ThAUJAS/H.E.D.A.S-Exoskeleton-glove-sensor-/image/45_wrist.png

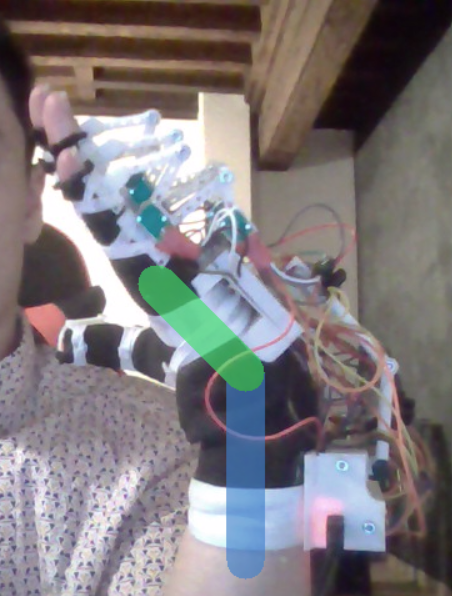
image/45_wrist.png
