ThAUJAS/H.E.D.A.S-Exoskeleton-glove-sensor-/image/_30_wrist.png

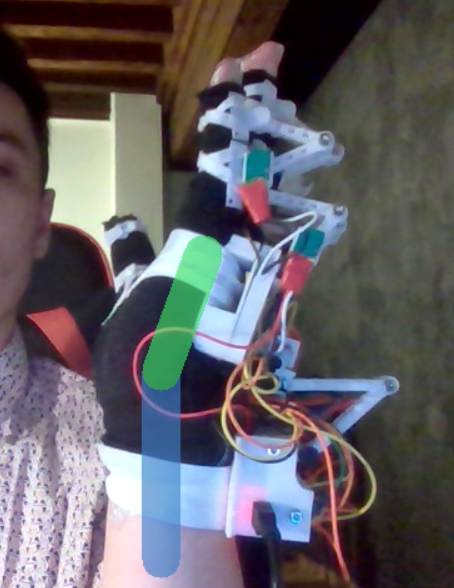
image/_30_wrist.png
