ThAUJAS/H.E.D.A.S-Exoskeleton-glove-sensor-/image/_45_wrist.png

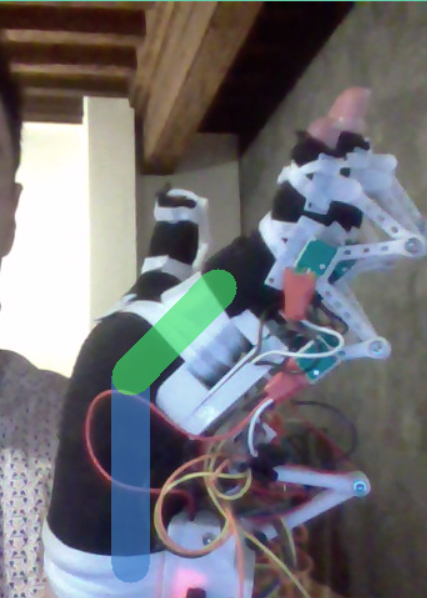
image/_45_wrist.png
