ThAUJAS/H.E.D.A.S-Exoskeleton-glove-sensor-/image/open_face.png

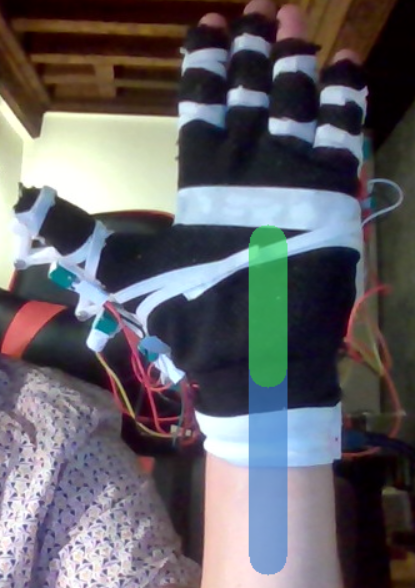
image/open_face.png
