ThAUJAS/H.E.D.A.S-Exoskeleton-glove-sensor-/STL/pin PIP v4.stl

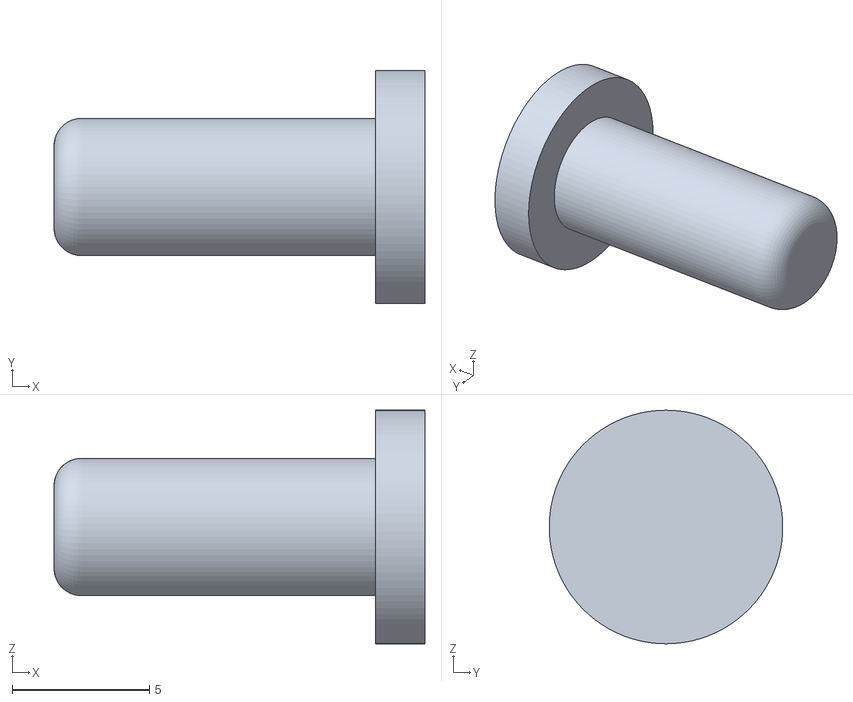
[picture p82: CAD file, 2021-08-12]
STL/pin PIP v4.stl
13.5 x 8.49 x 8.50
