ThAUJAS/H.E.D.A.S-Exoskeleton-glove-sensor-/STL/wire holder wrist z v6.stl

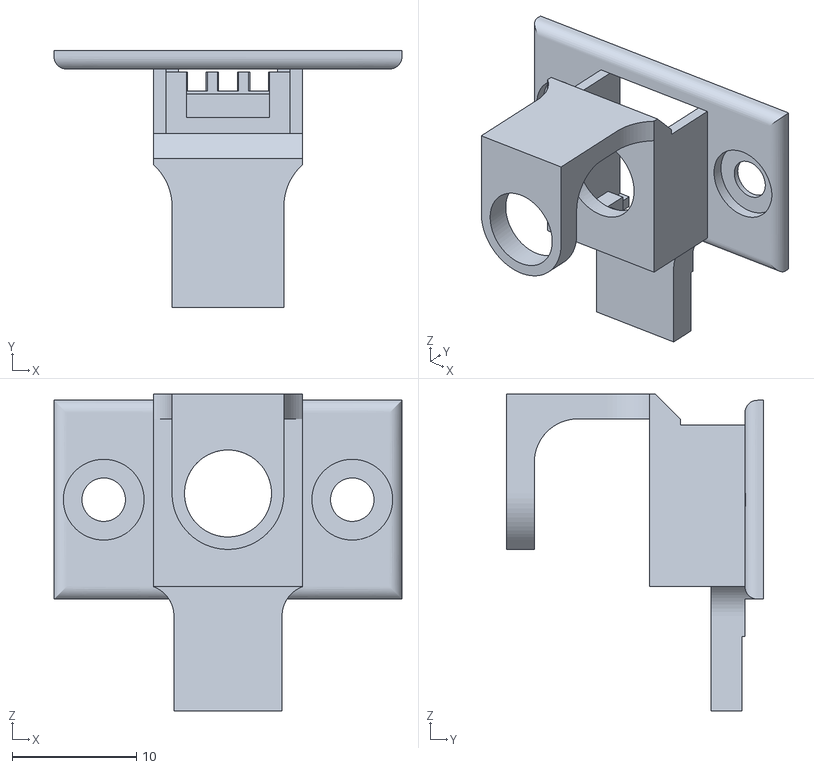
[picture p83: CAD file, 2021-08-12]
STL/wire holder wrist z v6.stl
28.0 x 20.7 x 25.5
