ThAUJAS/H.E.D.A.S-Exoskeleton-glove-sensor-/STL/cover arduino.stl

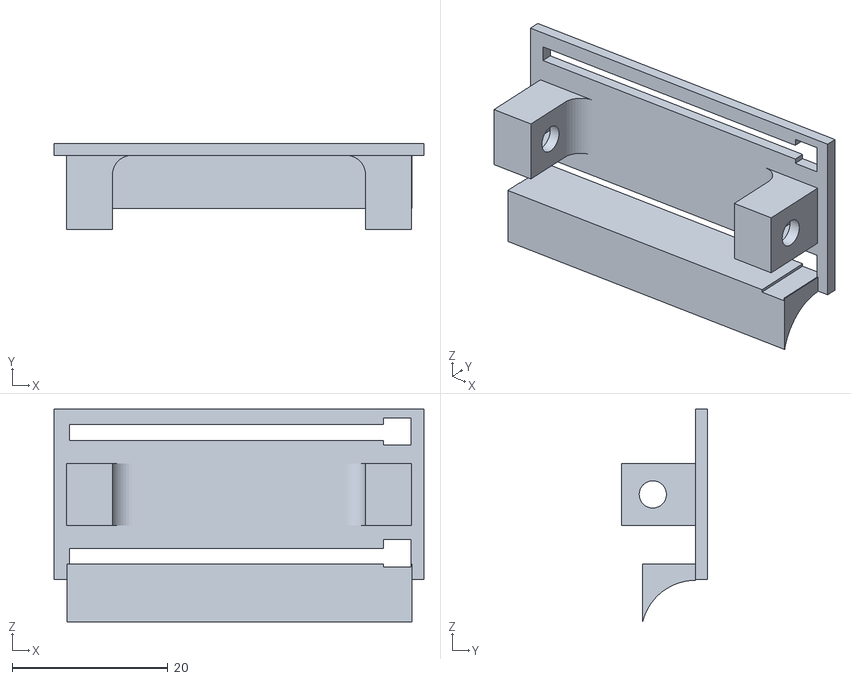
[picture p84: CAD file, 2021-08-12]
STL/cover arduino.stl
47.5 x 11.0 x 27.3
