ThAUJAS/H.E.D.A.S-Exoskeleton-glove-sensor-/STL/wire holder CMC z v5.stl

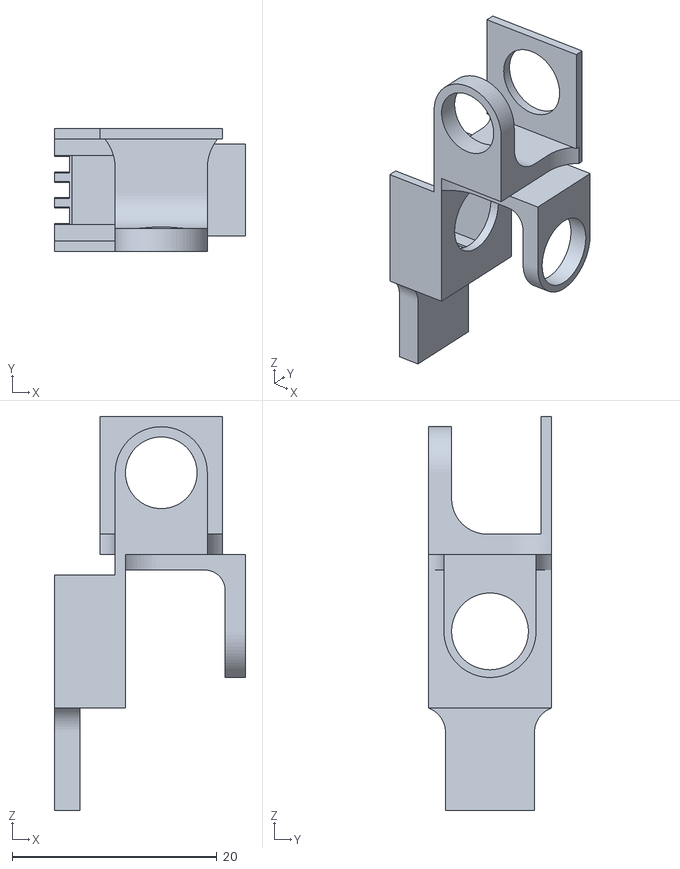
[picture p85: CAD file, 2021-08-12]
STL/wire holder CMC z v5.stl
18.7 x 12.0 x 38.5
