ThAUJAS/H.E.D.A.S-Exoskeleton-glove-sensor-/STL/uper plaque.stl

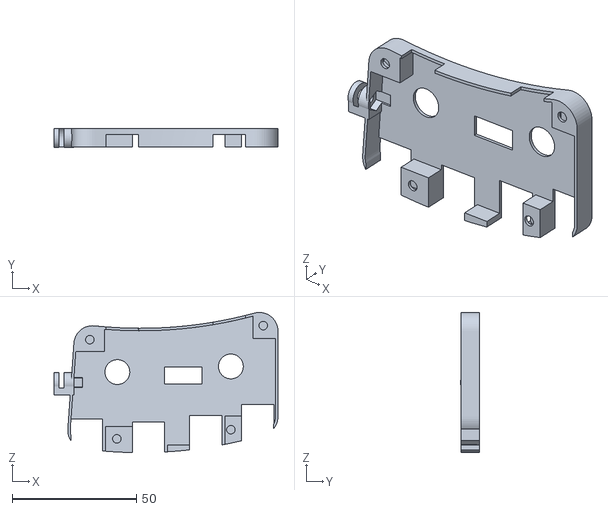
[picture p86: CAD file, 2021-08-12]
STL/uper plaque.stl
90.1 x 7.72 x 56.3
