ThAUJAS/H.E.D.A.S-Exoskeleton-glove-sensor-/STL/plaque.stl

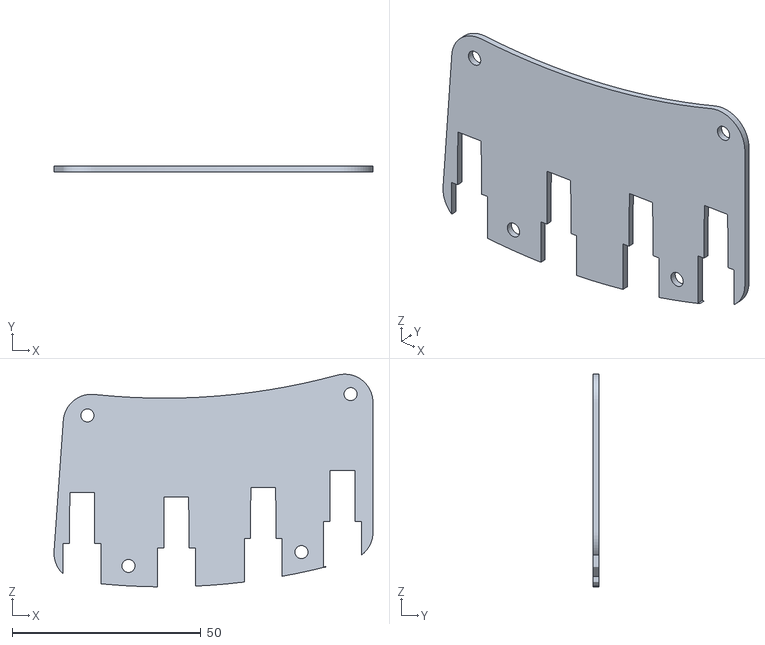
[picture p87: CAD file, 2021-08-12]
STL/plaque.stl
84.5 x 1.50 x 56.4
