ThAUJAS/H.E.D.A.S-Exoskeleton-glove-sensor-/STL/accuracy test.stl

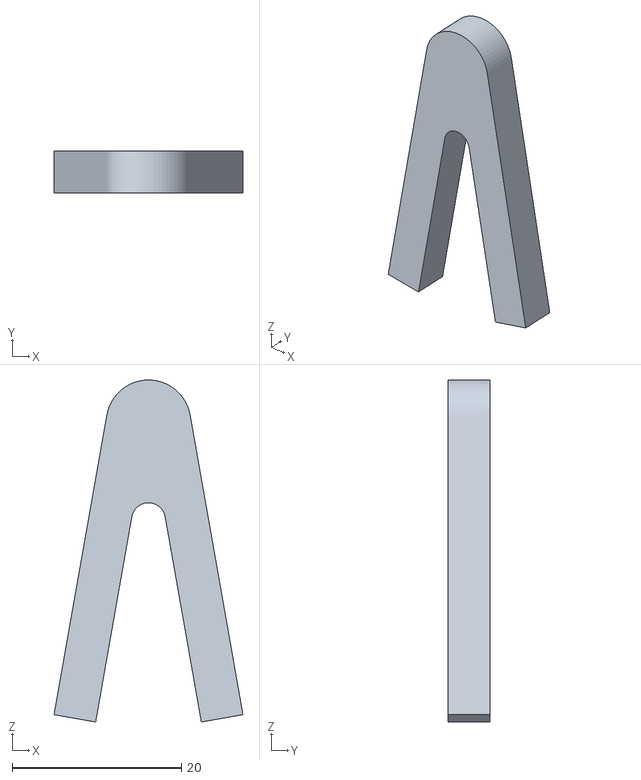
[picture p88: CAD file, 2021-08-12]
STL/accuracy test.stl
22.3 x 5.00 x 40.4
