ThAUJAS/H.E.D.A.S-Exoskeleton-glove-sensor-/STL/plaque bas.stl

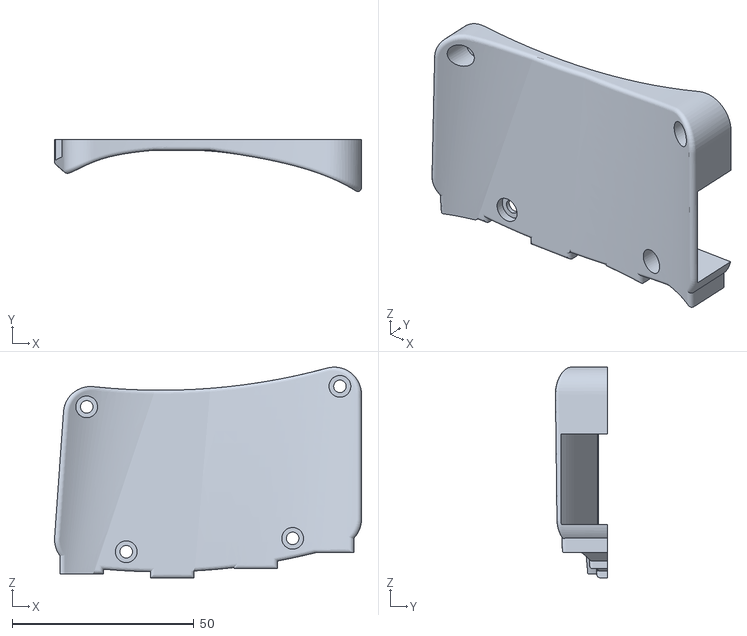
[picture p89: CAD file, 2021-08-12]
STL/plaque bas.stl
84.5 x 14.4 x 58.0
