ThAUJAS/H.E.D.A.S-Exoskeleton-glove-sensor-/STL/wire holder PIP v10.stl

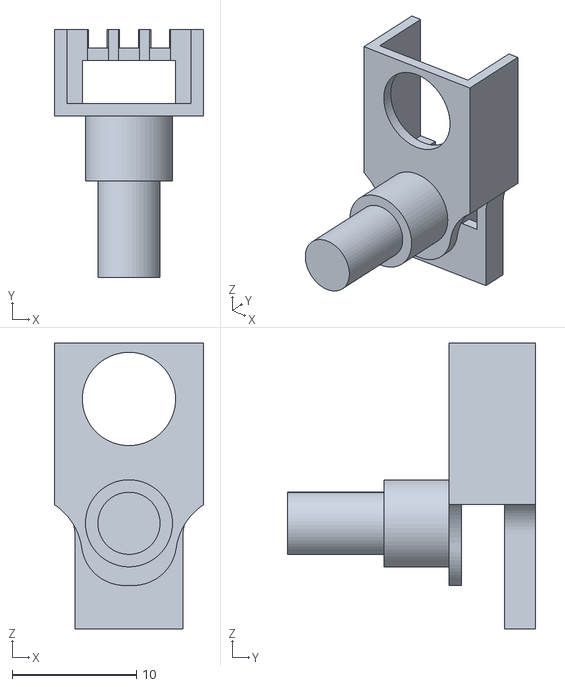
[picture p90: CAD file, 2021-08-12]
STL/wire holder PIP v10.stl
12.0 x 20.0 x 23.0
