ThAUJAS/H.E.D.A.S-Exoskeleton-glove-sensor-/STL/calibration 45.stl

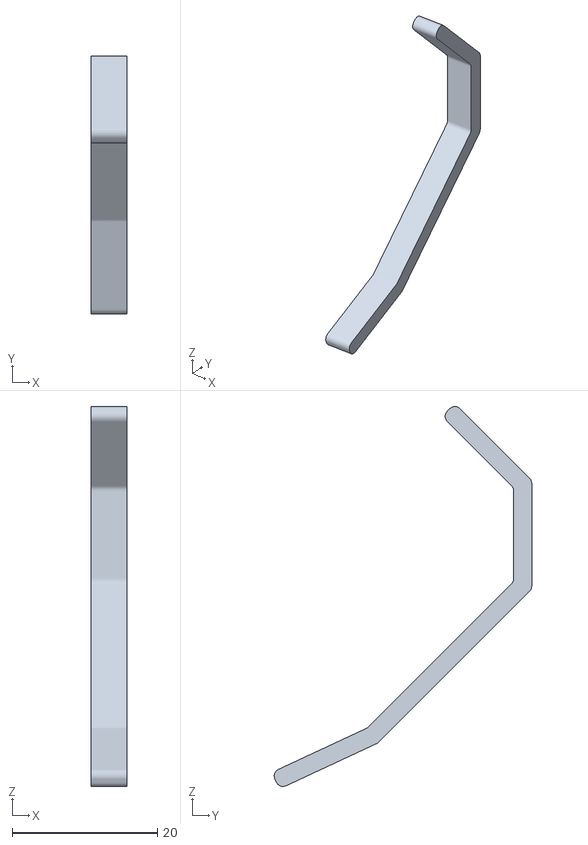
[picture p91: CAD file, 2021-08-12]
STL/calibration 45.stl
5.00 x 35.5 x 52.4
