ThAUJAS/H.E.D.A.S-Exoskeleton-glove-sensor-/STL/calibration 60.stl

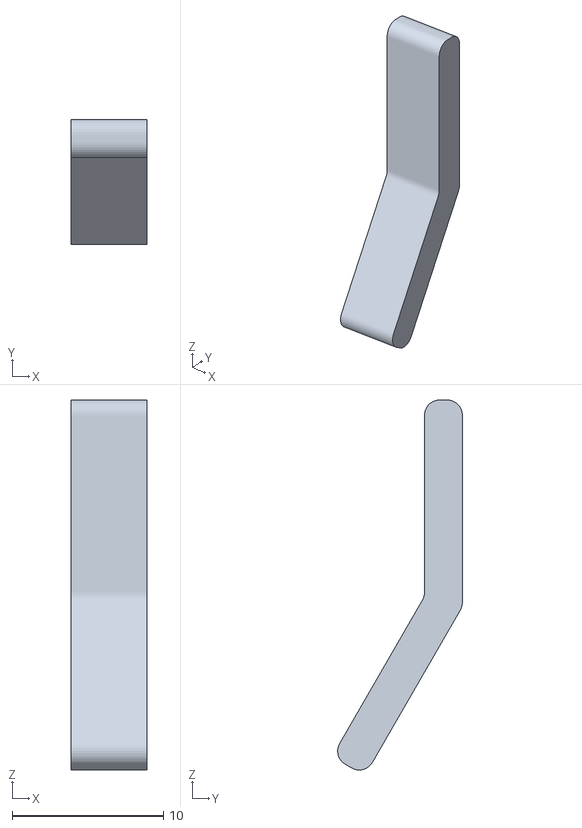
[picture p92: CAD file, 2021-08-12]
STL/calibration 60.stl
5.00 x 8.24 x 24.4
