ThAUJAS/H.E.D.A.S-Exoskeleton-glove-sensor-/STL/test barrr.stl

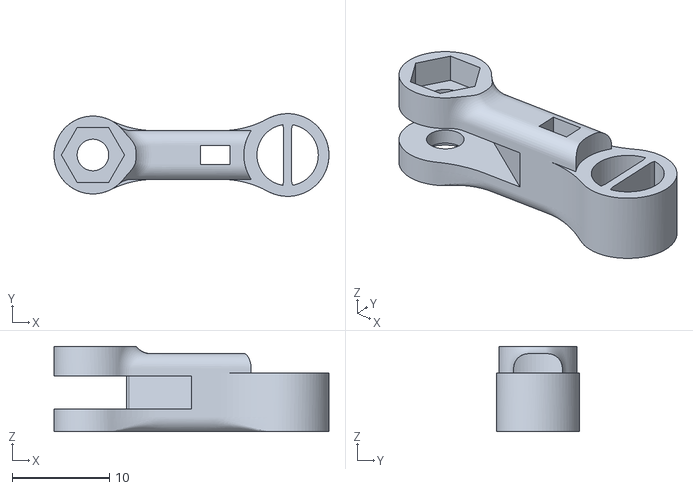
[picture p93: CAD file, 2021-08-12]
STL/test barrr.stl
28.2 x 8.50 x 8.75
