ThAUJAS/H.E.D.A.S-Exoskeleton-glove-sensor-/STL/wire holder MPC z v26.stl

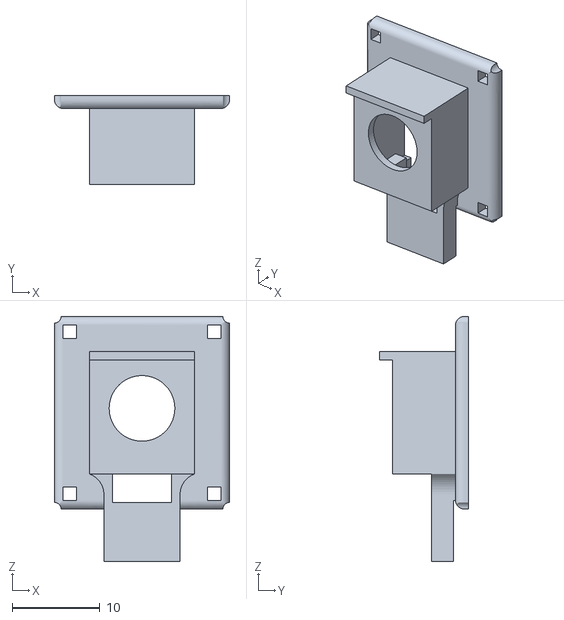
[picture p94: CAD file, 2021-08-12]
STL/wire holder MPC z v26.stl
20.0 x 10.2 x 28.0
