ThAUJAS/H.E.D.A.S-Exoskeleton-glove-sensor-/STL/wire holder wrist.stl

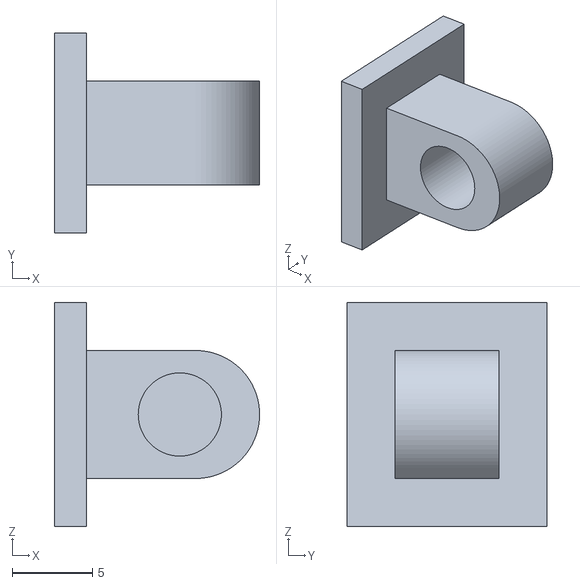
[picture p95: CAD file, 2021-08-12]
STL/wire holder wrist.stl
12.8 x 12.5 x 14.0
