ThAUJAS/H.E.D.A.S-Exoskeleton-glove-sensor-/STL/calibration 90.stl

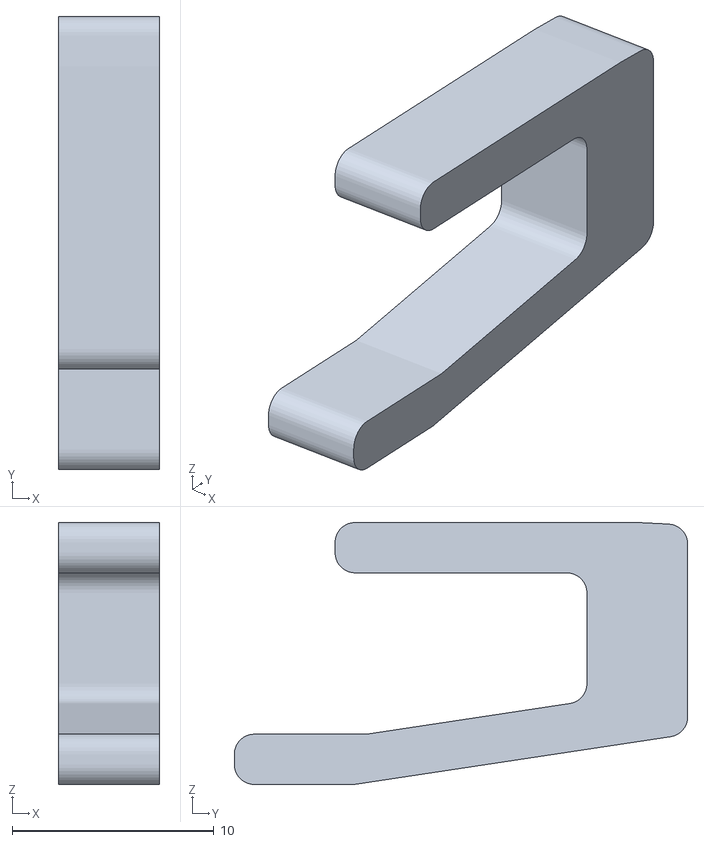
[picture p96: CAD file, 2021-08-12]
STL/calibration 90.stl
5.00 x 22.5 x 13.0
