ThAUJAS/H.E.D.A.S-Exoskeleton-glove-sensor-/STL/rev holder.stl

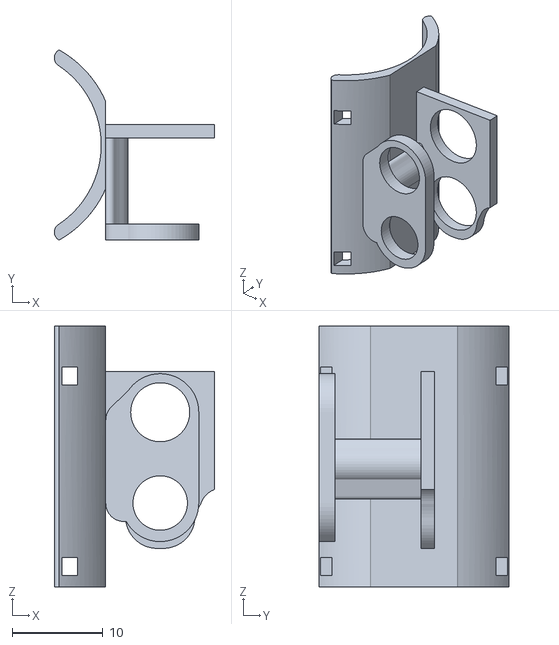
[picture p97: CAD file, 2021-08-12]
STL/rev holder.stl
17.7 x 21.0 x 28.8
