ThAUJAS/H.E.D.A.S-Exoskeleton-glove-sensor-/STL/mux box cover.stl

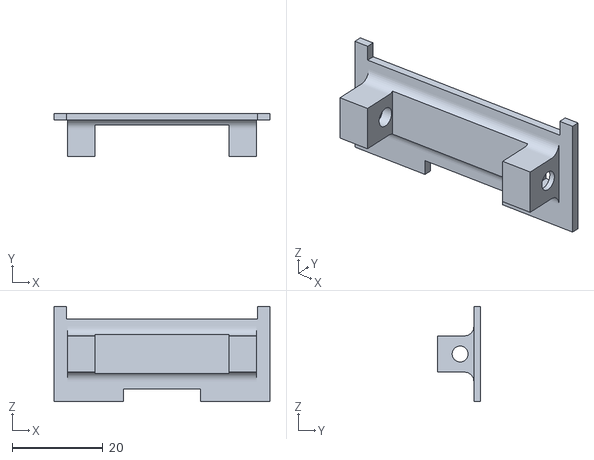
[picture p98: CAD file, 2021-08-12]
STL/mux box cover.stl
47.5 x 9.50 x 21.0
