ThAUJAS/H.E.D.A.S-Exoskeleton-glove-sensor-/STL/test bar cmc.stl

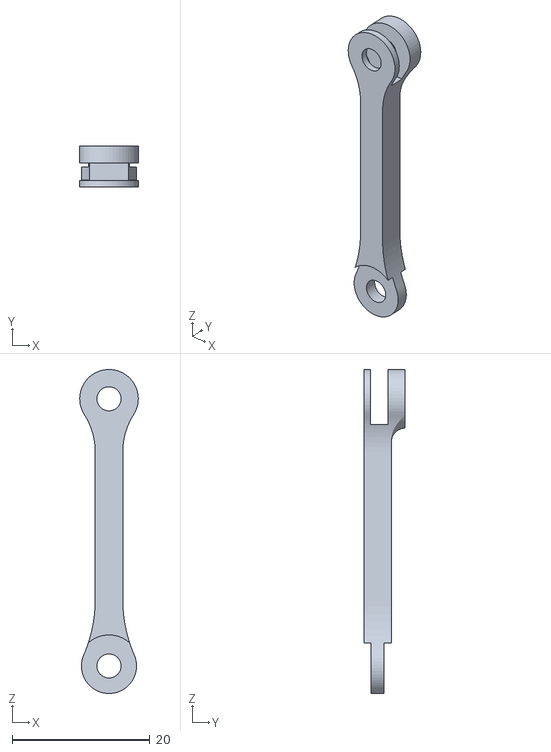
[picture p99: CAD file, 2021-08-12]
STL/test bar cmc.stl
8.50 x 6.00 x 47.0
