ThAUJAS/H.E.D.A.S-Exoskeleton-glove-sensor-/STL/bar connection wrist.stl

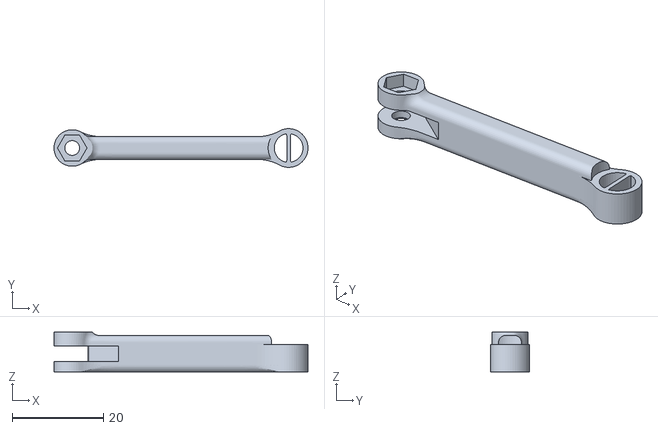
[picture p100: CAD file, 2021-08-12]
STL/bar connection wrist.stl
55.7 x 8.50 x 8.75
