ThAUJAS/H.E.D.A.S-Exoskeleton-glove-sensor-/STL/CE3_plaque.3mf

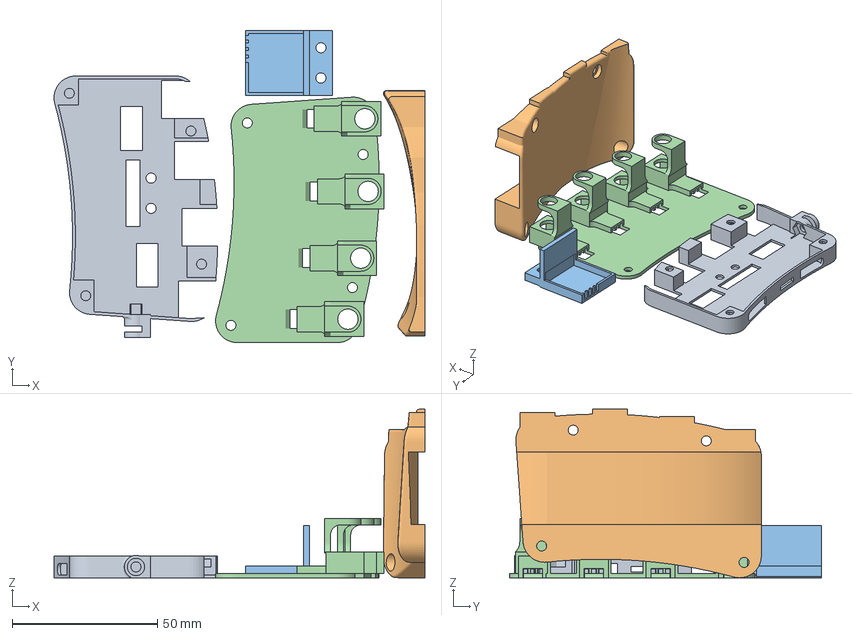
[picture p101: CAD file, 2021-08-12]
STL/CE3_plaque.3mf
127.7 x 107.5 x 58.0 mm
plaque up.stl
plaque bas.stl
imu box.stl
plaque main v21.stl
