ThAUJAS/H.E.D.A.S-Exoskeleton-glove-sensor-/STL/test cmc x bar.stl

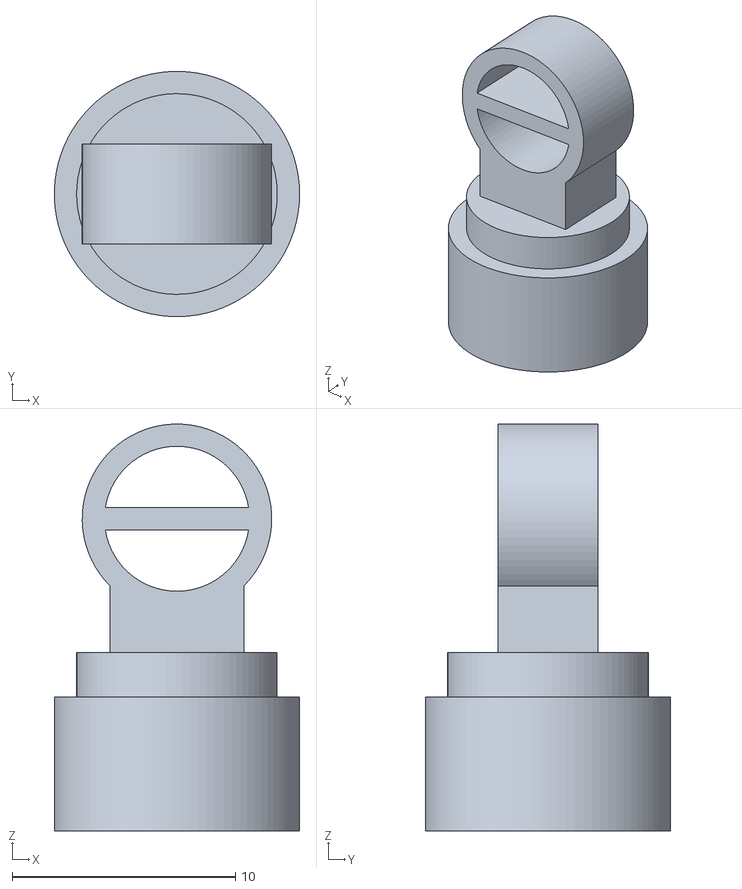
[picture p102: CAD file, 2021-08-12]
STL/test cmc x bar.stl
11.0 x 11.0 x 18.2
