ThAUJAS/H.E.D.A.S-Exoskeleton-glove-sensor-/STL/test bar 2.stl

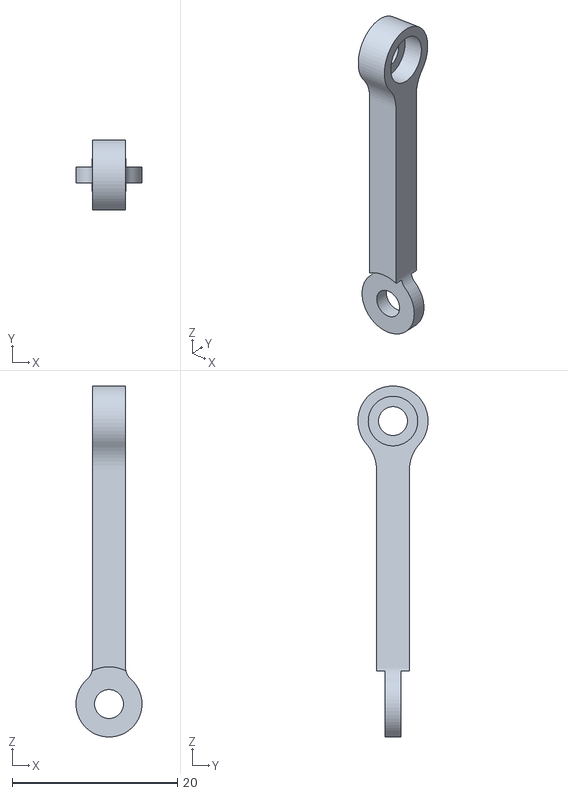
[picture p103: CAD file, 2021-08-12]
STL/test bar 2.stl
8.00 x 8.49 x 42.5
