ThAUJAS/H.E.D.A.S-Exoskeleton-glove-sensor-/STL/bar connection v49.stl

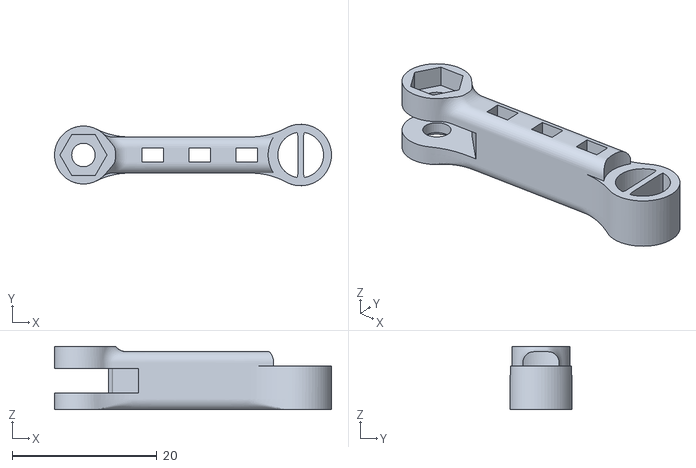
[picture p104: CAD file, 2021-08-12]
STL/bar connection v49.stl
38.2 x 8.50 x 8.75
